JPFunk/JP_Capstone/JP_Capstone_Support_Files/JP_Capstone_3D/3D_Maps/crystal-clear-terrazzo-glass-346829.webp

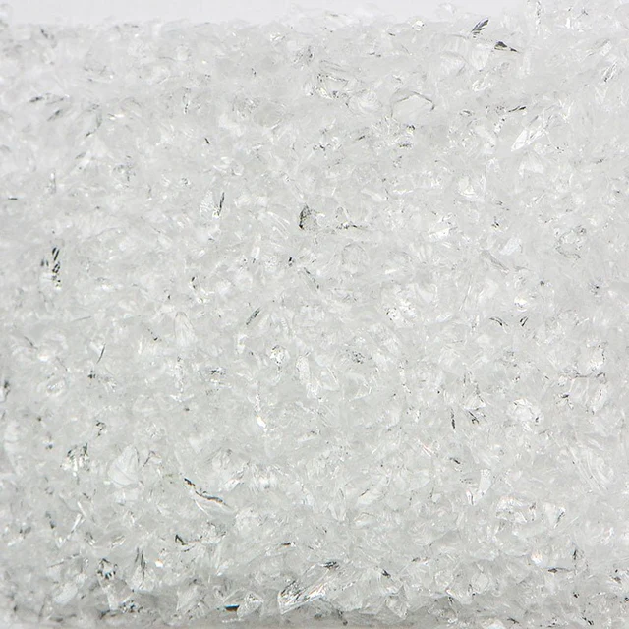
JP_Capstone_Support_Files/JP_Capstone_3D/3D_Maps/crystal-clear-terrazzo-glass-346829.webp
