JPFunk/JP_Capstone/JP_Capstone_Support_Files/JP_Capstone_3D/3D_Maps/crystal-clear-terrazzo-glass-661629.jpg

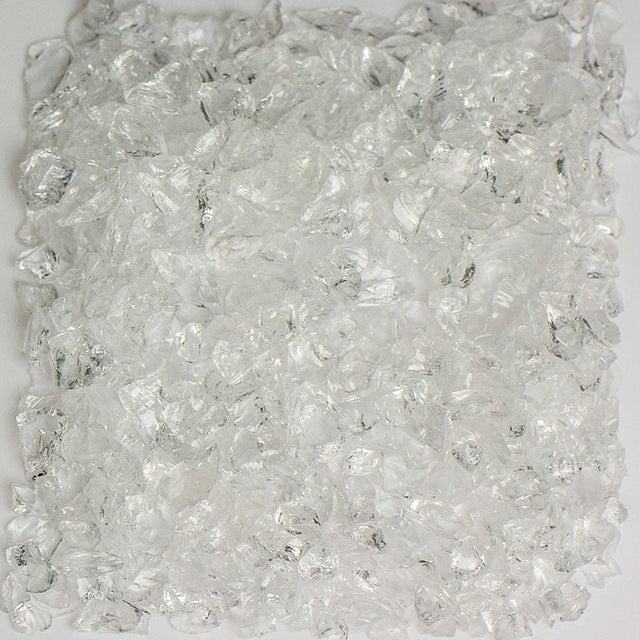
JP_Capstone_Support_Files/JP_Capstone_3D/3D_Maps/crystal-clear-terrazzo-glass-661629.jpg
