JPFunk/JP_Capstone/JP_Capstone_Support_Files/JP_Capstone_3D/3D_Maps/JP_Oracle_WaterPanel.jpg

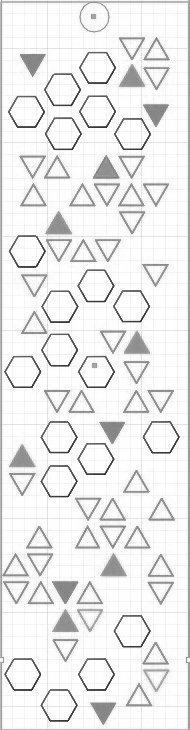
JP_Capstone_Support_Files/JP_Capstone_3D/3D_Maps/JP_Oracle_WaterPanel.jpg
