JPFunk/JP_Capstone/JP_Capstone_Support_Files/JP_Capstone_3D/3D_Maps/s-l1600.gif

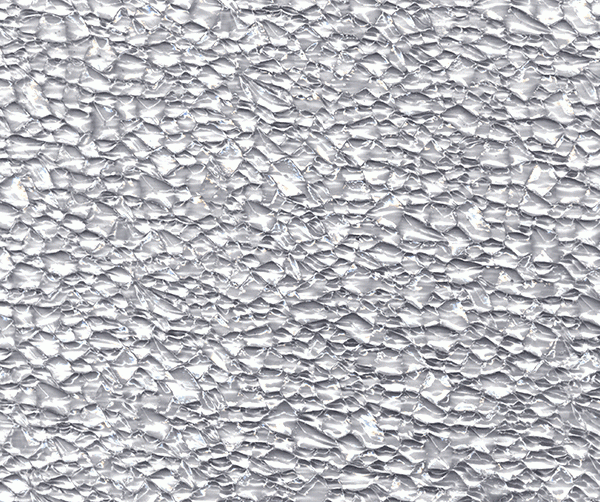
JP_Capstone_Support_Files/JP_Capstone_3D/3D_Maps/s-l1600.gif
