JPFunk/JP_Capstone/JP_Capstone_Support_Files/JP_Capstone_3D/JP_Oracle_Solidworks/JP_Oracle_Speaker_Ring.JPG

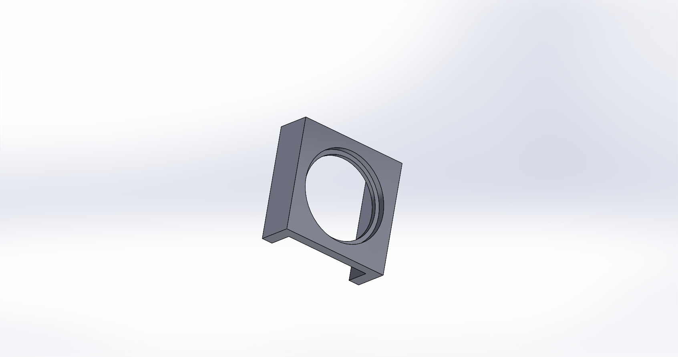
JP_Capstone_Support_Files/JP_Capstone_3D/JP_Oracle_Solidworks/JP_Oracle_Speaker_Ring.JPG
