JPFunk/JP_Capstone/JP_Capstone_Support_Files/JP_Capstone_3D/JP_Oracle_V2.jpg

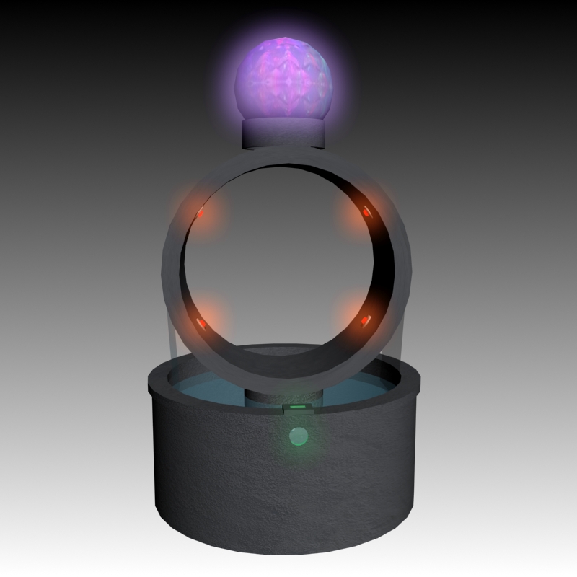
JP_Capstone_Support_Files/JP_Capstone_3D/JP_Oracle_V2.jpg
