JPFunk/JP_Capstone/JP_Capstone_Support_Files/JP_Oracle_Fountain.png

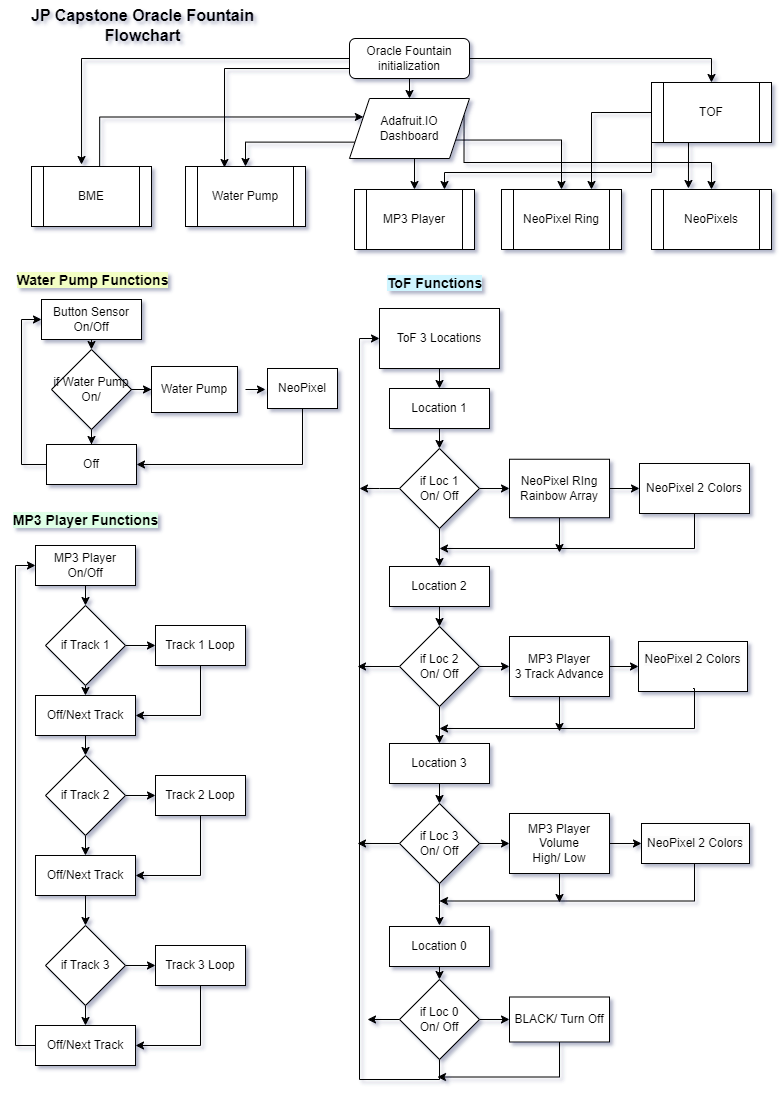
JP_Capstone_Support_Files/JP_Oracle_Fountain.png
