JPFunk/JP_Capstone/JP_Oracle_Fountain/JP_Oracle_FountainV1_bb.jpg

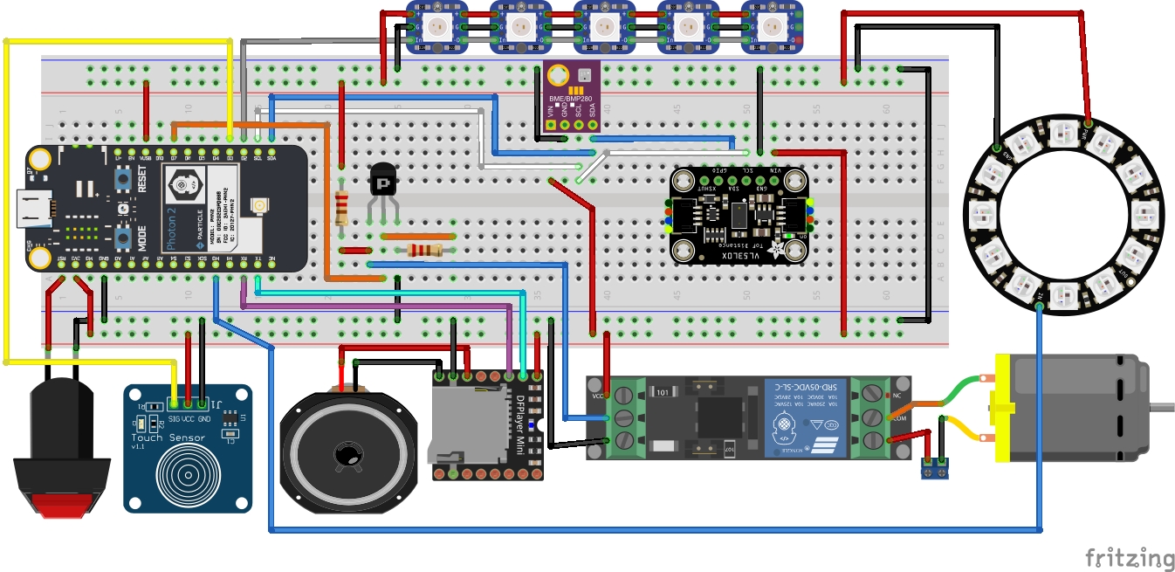
JP_Oracle_Fountain/JP_Oracle_FountainV1_bb.jpg
