JPFunk/JP_Capstone/JP_Capstone_Support_Files/JP_Capstone_3D/JP_Oracle_Solidworks/Solidworks issue.jpg

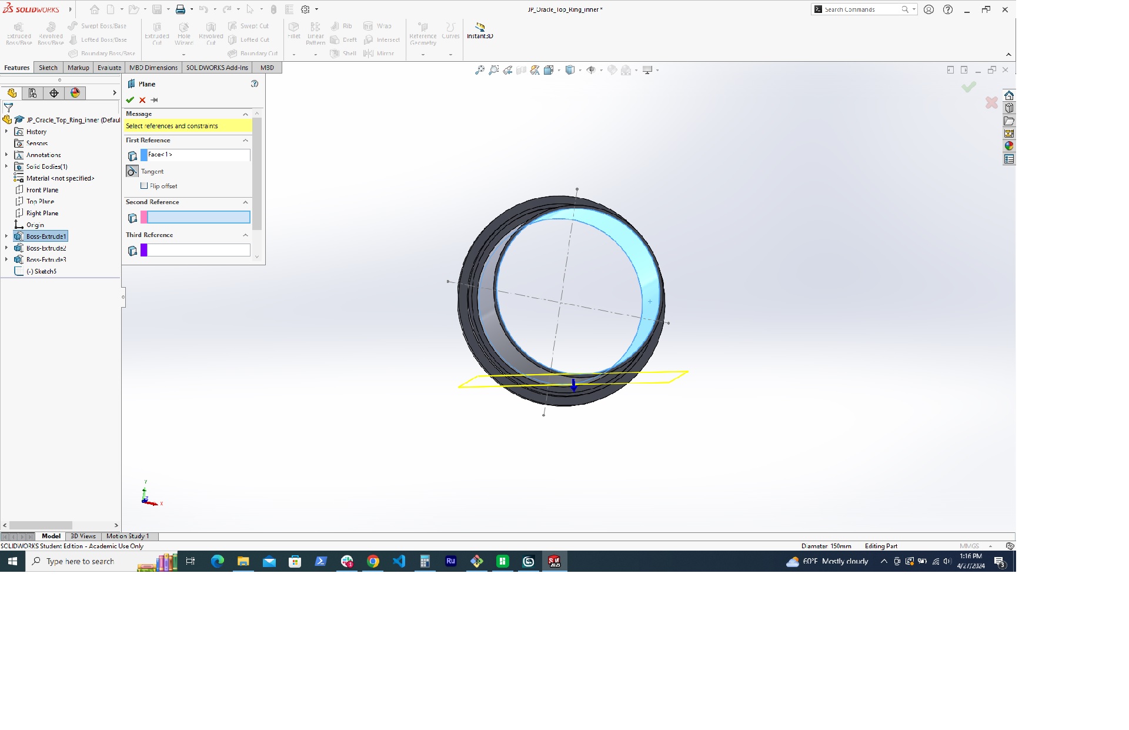
JP_Capstone_Support_Files/JP_Capstone_3D/JP_Oracle_Solidworks/Solidworks issue.jpg
